balazsbencs/midi-pedal/docs/ui-concepts/03-performance-focus.png

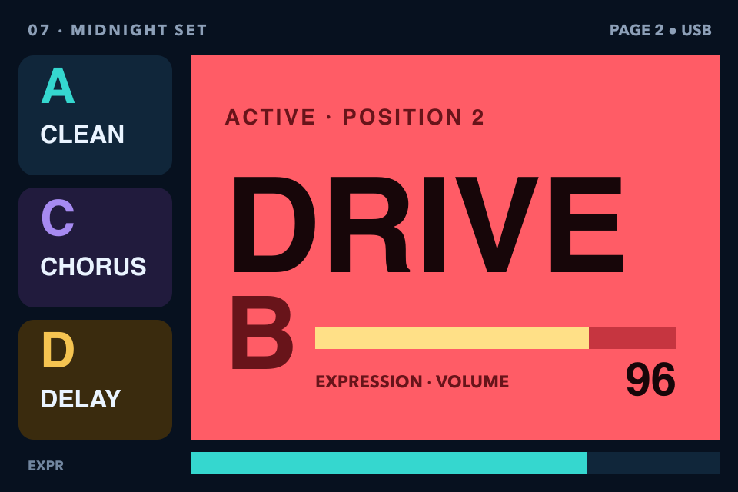
docs/ui-concepts/03-performance-focus.png
