balazsbencs/midi-pedal/firmware/src/hal/ports.hpp

#pragma once

#include <array>
#include <cstddef>
#include <cstdint>

#include "../core/config_types.hpp"

namespace midi {

struct LiveView {
  std::uint8_t bank{};
  std::uint8_t page{};
  AsciiString<20> bankName{};
  std::array<std::uint8_t, 4> positions{};
  // Physical switch state presented independently from persistent toggle
  // positions, so input wiring and action handling are visible on the pedal.
  std::uint8_t pressedMask{};
  std::array<PositionView, 4> selectedPositions{};
  bool expressionAvailable{};
  std::uint8_t expressionValue{};
  AsciiString<12> expressionLabel{};
  bool usbConnected{};
  bool configurationError{};
  bool queueOverflow{};
  bool watchdogReset{};
};

struct Clock {
  virtual ~Clock() = default;
  virtual std::uint32_t now_ms() const = 0;
};

struct RelayPort {
  virtual ~RelayPort() = default;
  virtual void set(std::uint8_t contact, bool closed) = 0;
};

struct MidiPort {
  virtual ~MidiPort() = default;
  virtual bool enqueue(Destination destination, MidiMessage message) = 0;
};

struct DisplayPort {
  virtual ~DisplayPort() = default;
  virtual void present(const LiveView& view) = 0;
};

// Hardware-facing read-only configuration status hook. The persistent image
// implementation lives in core/config_store.hpp and intentionally owns the
// ConfigStore name.
struct ConfigReader {
  virtual ~ConfigReader() = default;
  virtual bool read_active_config() = 0;
};

struct DiagnosticPort {
  virtual ~DiagnosticPort() = default;
  virtual void record(std::uint16_t code) = 0;
};

struct ControllerPorts {
  virtual ~ControllerPorts() = default;
  virtual void relay_set(std::uint8_t contact, bool closed) = 0;
  virtual bool read_active_config() = 0;
  virtual void show_boot_status() = 0;
};

}  // namespace midi
